FabLabWgtn/Lampshade/images/image1.jpg

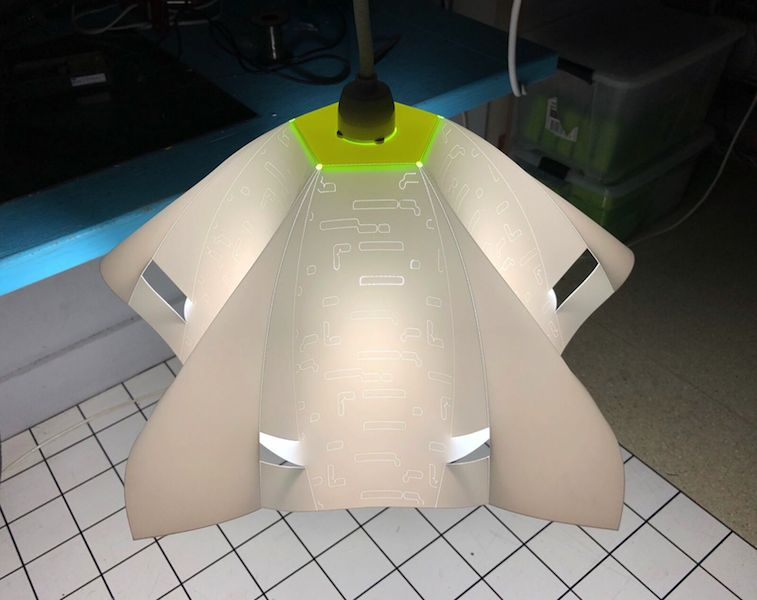
images/image1.jpg
