FabLabWgtn/Lampshade/images/image2.jpg

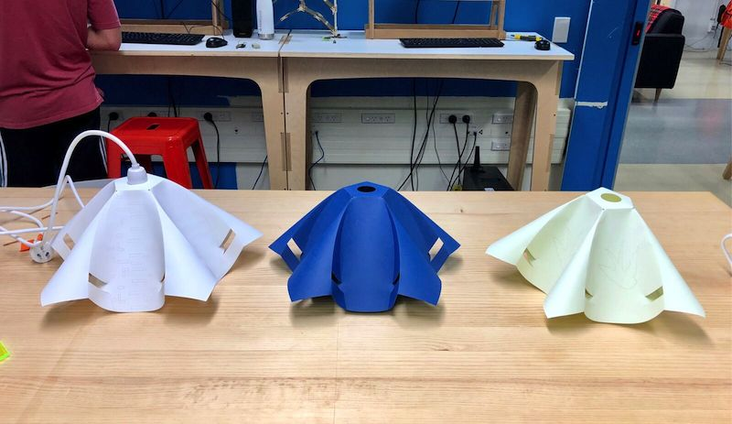
images/image2.jpg
