FabLabWgtn/Lampshade/images/image13.jpg

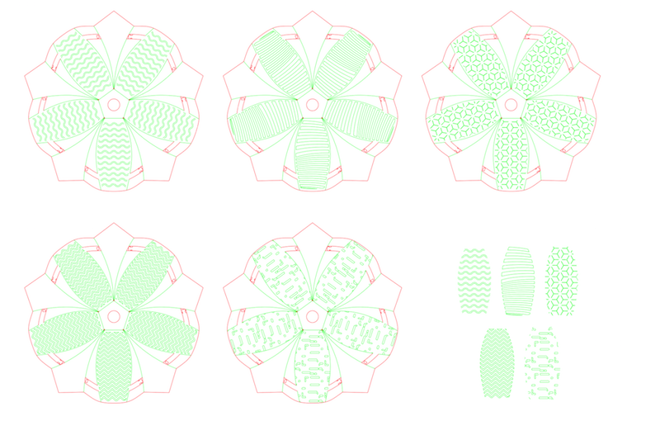
images/image13.jpg
